Daemon19/revisi-grup-f/mechanical/Demo/FP (Sebelum Revisi)/FP V2 Mounting Plate.stp

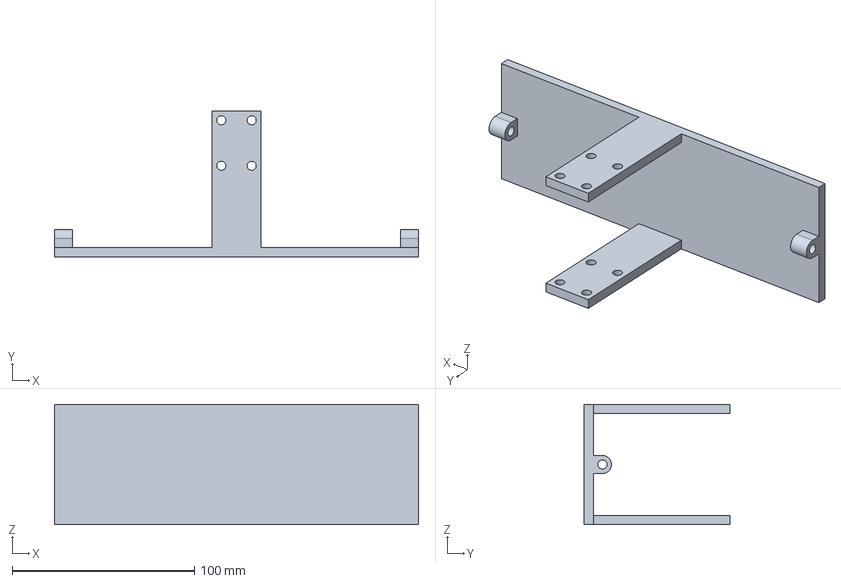
[picture p15: CAD file, 2026-03-05]
mechanical/Demo/FP (Sebelum Revisi)/FP V2 Mounting Plate.stp
200.0 x 80.0 x 66.0 mm
