Daemon19/revisi-grup-f/mechanical/Demo/FP (Sebelum Revisi)/Servo/MG_996R v1.stp

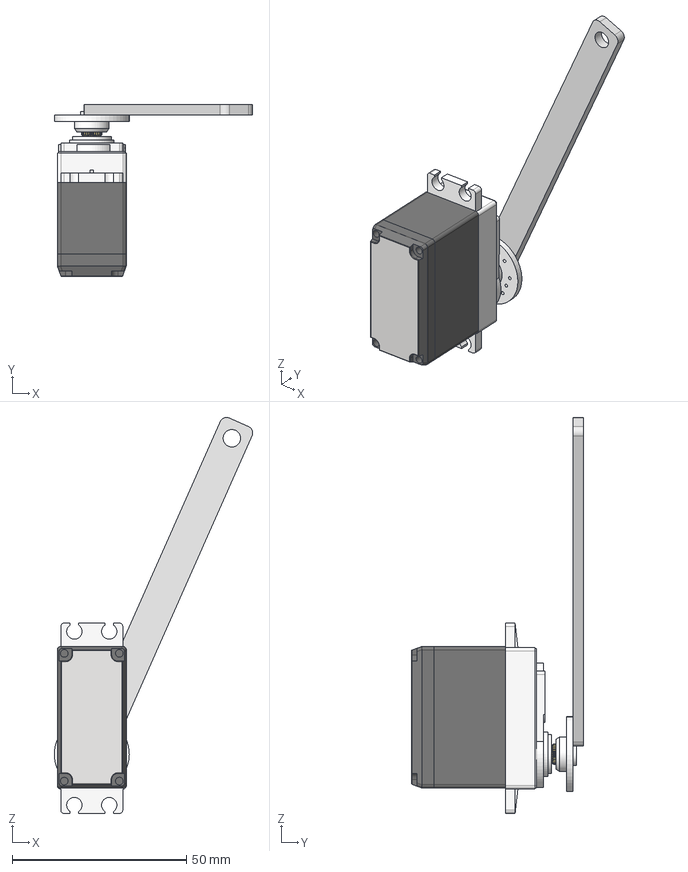
[picture p16: CAD file, 2026-03-05]
mechanical/Demo/FP (Sebelum Revisi)/Servo/MG_996R v1.stp
56.9 x 49.3 x 113.5 mm
Top
Medio
Base
Eje
Acople circular
FP V2 Servo Arm v2
