Daemon19/revisi-grup-f/mechanical/Demo/FP (Sebelum Revisi)/FP V2 Mounting Claw.stp

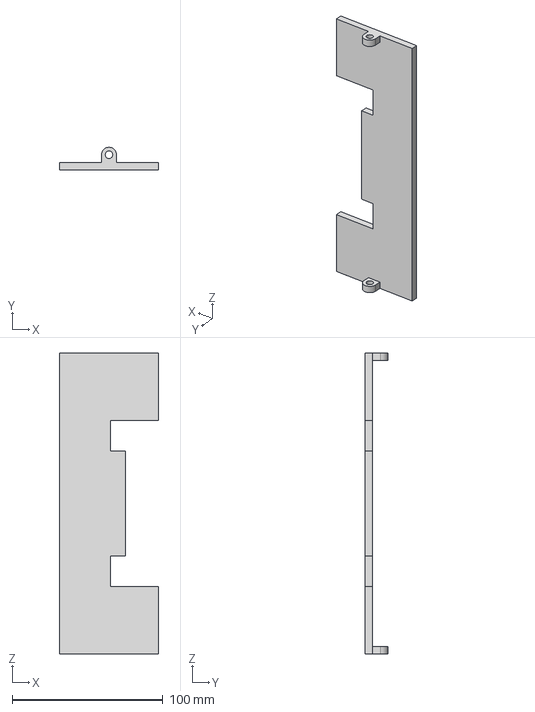
[picture p17: CAD file, 2026-03-05]
mechanical/Demo/FP (Sebelum Revisi)/FP V2 Mounting Claw.stp
66.0 x 15.0 x 200.0 mm
