Daemon19/revisi-grup-f/mechanical/Demo/FP (Sebelum Revisi)/fp v2 servo Mounting.stp

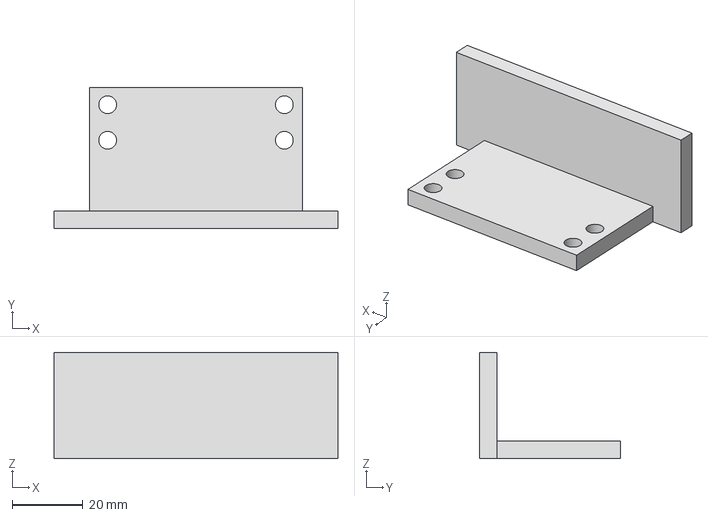
[picture p18: CAD file, 2026-03-05]
mechanical/Demo/FP (Sebelum Revisi)/fp v2 servo Mounting.stp
80.0 x 39.8 x 30.0 mm
