Daemon19/revisi-grup-f/mechanical/Demo/FP (Sebelum Revisi)/FP V2 Z Axis connector.stp

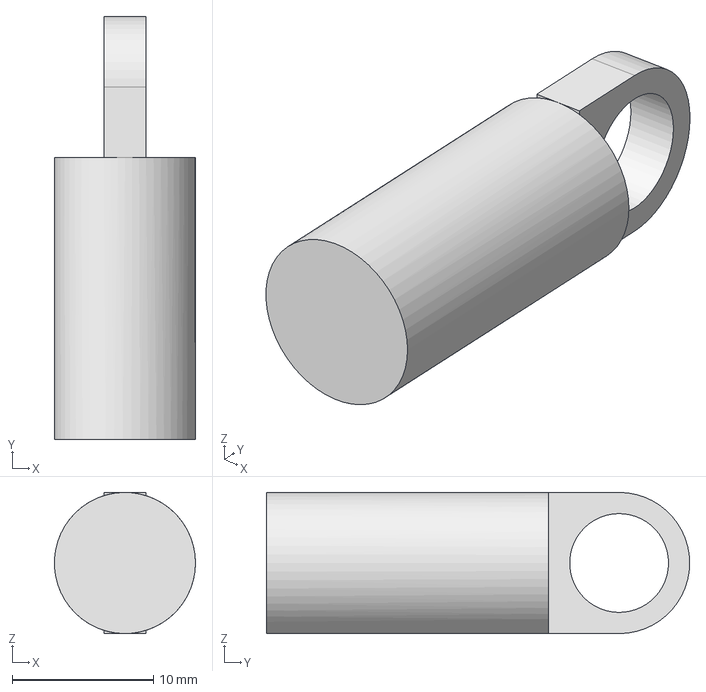
[picture p19: CAD file, 2026-03-05]
mechanical/Demo/FP (Sebelum Revisi)/FP V2 Z Axis connector.stp
9.99 x 30.0 x 10.0 mm
