Daemon19/revisi-grup-f/mechanical/Demo/FP (Sebelum Revisi)/FP V2 Claw_Side.stp

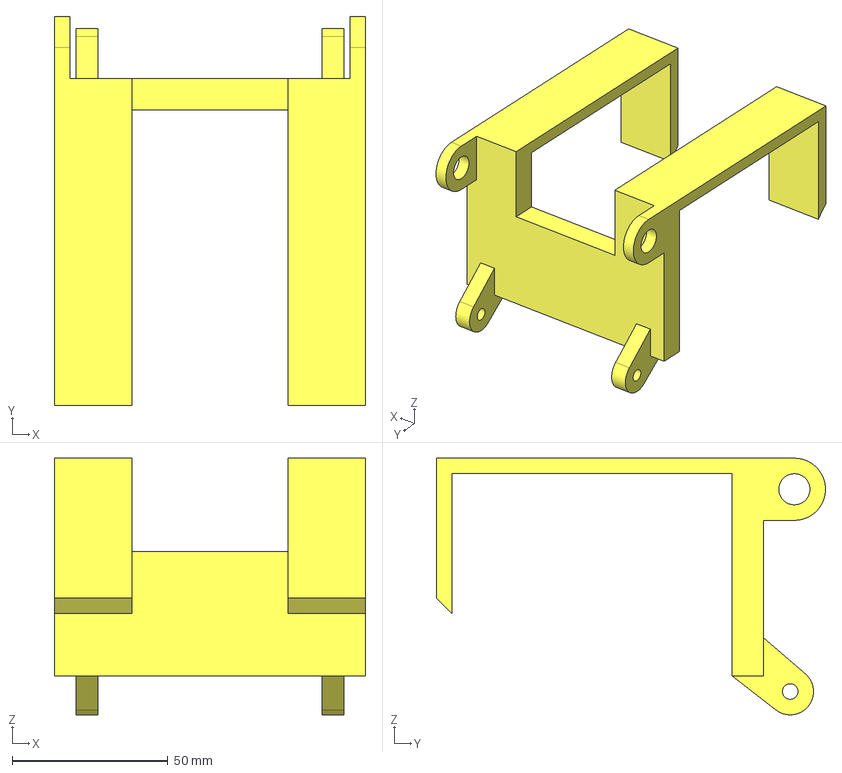
[picture p20: CAD file, 2026-03-05]
mechanical/Demo/FP (Sebelum Revisi)/FP V2 Claw_Side.stp
100.0 x 125.0 x 82.5 mm
