Daemon19/revisi-grup-f/mechanical/Demo/FP (Sebelum Revisi)/FP V2 Claw Connector.stp

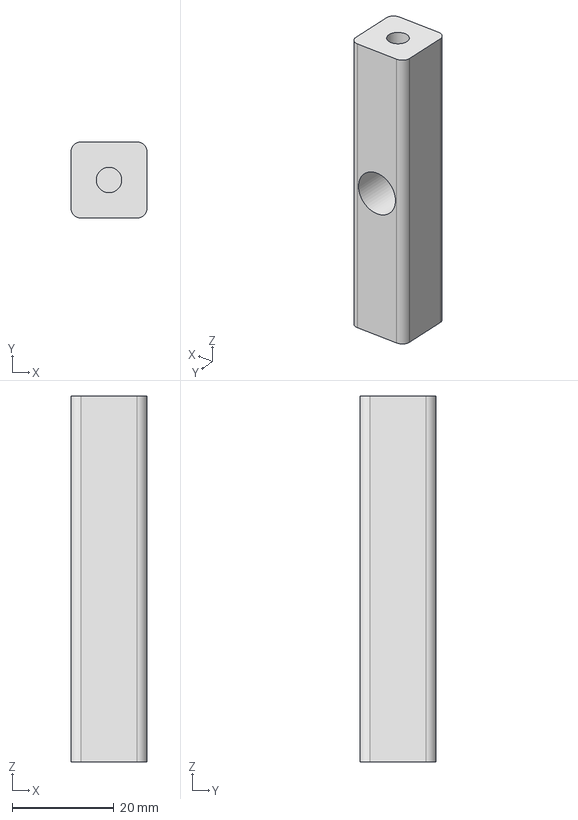
[picture p21: CAD file, 2026-03-05]
mechanical/Demo/FP (Sebelum Revisi)/FP V2 Claw Connector.stp
15.0 x 15.0 x 72.0 mm
