Daemon19/revisi-grup-f/mechanical/Demo/FP (Sebelum Revisi)/FP V2 Batang Penggerak.stp

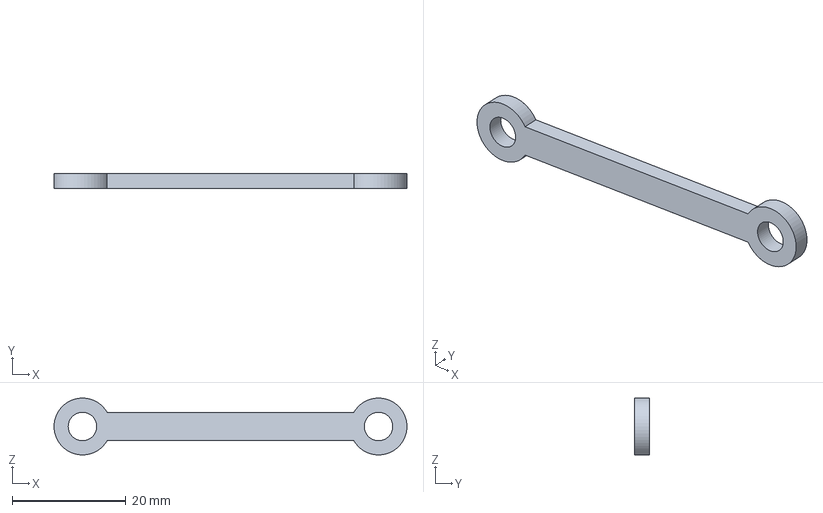
[picture p22: CAD file, 2026-03-05]
mechanical/Demo/FP (Sebelum Revisi)/FP V2 Batang Penggerak.stp
62.0 x 2.70 x 9.99 mm
