Daemon19/revisi-grup-f/mechanical/Demo/FP (Sebelum Revisi)/FP V2 Arm Connector.stp

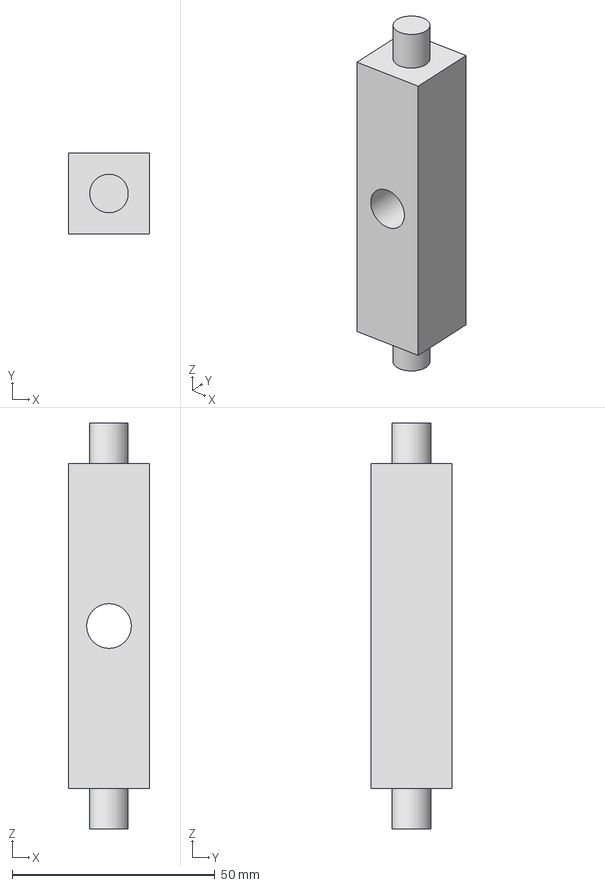
[picture p23: CAD file, 2026-03-05]
mechanical/Demo/FP (Sebelum Revisi)/FP V2 Arm Connector.stp
20.0 x 20.0 x 100.0 mm
