Daemon19/revisi-grup-f/mechanical/Demo/FP (Sebelum Revisi)/FP V2 Shaft.stp

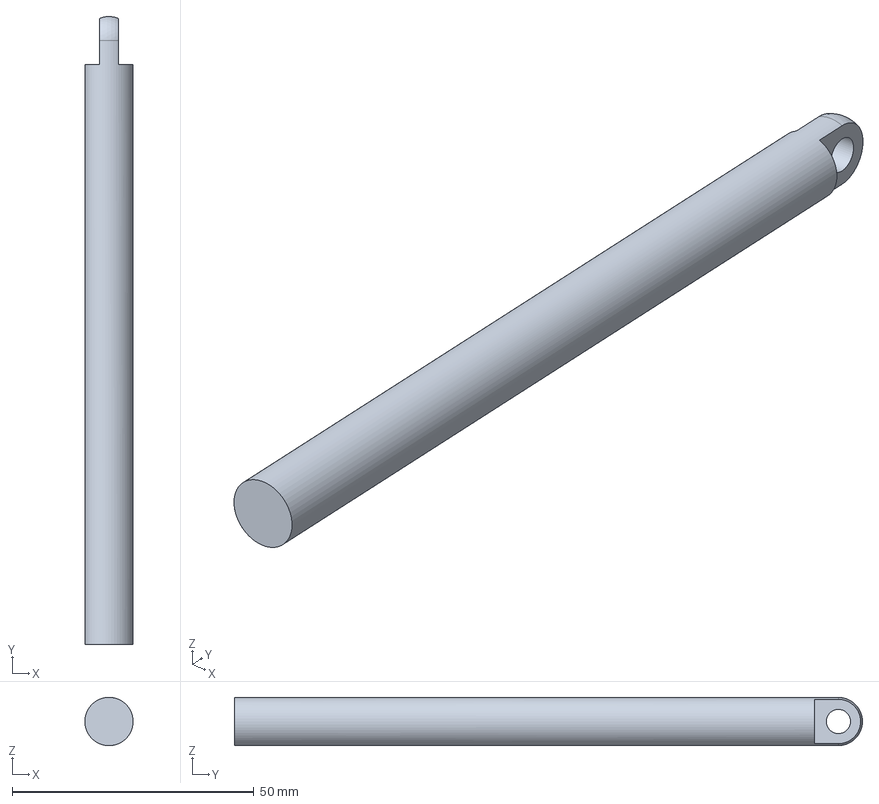
[picture p24: CAD file, 2026-03-05]
mechanical/Demo/FP (Sebelum Revisi)/FP V2 Shaft.stp
9.99 x 130.0 x 10.00 mm
