Daemon19/revisi-grup-f/mechanical/Demo/FP (Sebelum Revisi)/FP V2 Spring beam Short.stp

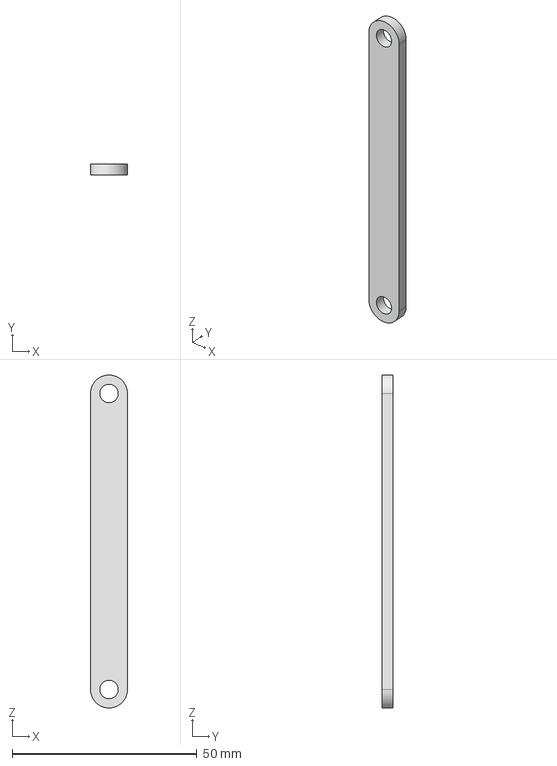
[picture p25: CAD file, 2026-03-05]
mechanical/Demo/FP (Sebelum Revisi)/FP V2 Spring beam Short.stp
10.0 x 3.00 x 90.0 mm
